Ning0612/Pi-Paper-Clock/tests/test_discord_notifier.py

import importlib.util
import json
import os
import sys
import tempfile
import types
import unittest
from pathlib import Path


class DiscordNotifierTests(unittest.TestCase):
    @classmethod
    def setUpClass(cls):
        names = ("network", "config_manager")
        cls.original_modules = {name: sys.modules.get(name) for name in names}

        network = types.ModuleType("network")
        network.STA_IF = 0
        network.WLAN = lambda _interface: types.SimpleNamespace(isconnected=lambda: False)
        sys.modules["network"] = network

        config_module = types.ModuleType("config_manager")
        config_module.config_manager = types.SimpleNamespace(
            get_global=lambda _key, default="": default,
            get=lambda _key, default=None: default,
        )
        sys.modules["config_manager"] = config_module

        source = Path(__file__).resolve().parents[1] / "src" / "discord_notifier.py"
        spec = importlib.util.spec_from_file_location("discord_notifier_test", source)
        cls.module = importlib.util.module_from_spec(spec)
        spec.loader.exec_module(cls.module)

    @classmethod
    def tearDownClass(cls):
        for name, module in cls.original_modules.items():
            if module is None:
                sys.modules.pop(name, None)
            else:
                sys.modules[name] = module

    def test_delivery_blocked_distinguishes_config_from_link_failures(self):
        config = sys.modules["config_manager"].config_manager
        original_get_global = config.get_global
        original_wlan = sys.modules["network"].WLAN
        try:
            config.get_global = lambda _key, default="": ""
            self.assertEqual(self.module.delivery_blocked(), "nowebhook")

            config.get_global = lambda _key, default="": "https://discord.com/api/webhooks/x/y"
            sys.modules["network"].WLAN = lambda _i: types.SimpleNamespace(
                isconnected=lambda: False
            )
            self.assertEqual(self.module.delivery_blocked(), "offline")

            sys.modules["network"].WLAN = lambda _i: types.SimpleNamespace(
                isconnected=lambda: True
            )
            self.assertEqual(self.module.delivery_blocked(), "")
        finally:
            config.get_global = original_get_global
            sys.modules["network"].WLAN = original_wlan

    def test_headroom_probe_reports_available_contiguous_block(self):
        self.assertTrue(self.module.has_tls_headroom(1024))
        self.assertEqual(self.module.largest_contiguous_block(4096), 4096)

    def test_diag_record_appends_and_trims_without_unbounded_growth(self):
        original_file = self.module.DIAG_FILE
        original_max = self.module.MAX_DIAG_BYTES
        with tempfile.TemporaryDirectory() as directory:
            self.module.DIAG_FILE = str(Path(directory) / "diag.log")
            self.module.MAX_DIAG_BYTES = 256
            try:
                for index in range(120):
                    self.module.diag_record("fail", "n={}".format(index))

                size = os.stat(self.module.DIAG_FILE).st_size
                self.assertLessEqual(size, self.module.MAX_DIAG_BYTES * 2)
                with open(self.module.DIAG_FILE) as handle:
                    lines = [line for line in handle.read().split("\n") if line]
                # Trimming drops the oldest half; the newest entry always survives.
                self.assertTrue(lines[-1].endswith("n=119"))
                self.assertIn("fail", lines[-1])
            finally:
                self.module.DIAG_FILE = original_file
                self.module.MAX_DIAG_BYTES = original_max

    def test_diag_record_never_raises_when_path_is_unwritable(self):
        original_file = self.module.DIAG_FILE
        self.module.DIAG_FILE = str(Path("no-such-dir") / "nested" / "diag.log")
        try:
            self.module.diag_record("fail", "unwritable")
        finally:
            self.module.DIAG_FILE = original_file

    def test_json_payload_escapes_controls_and_keeps_utf8_emoji(self):
        message = 'quote " slash \\ newline\n tab\t 中文🟦'
        payload = self.module._discord_payload(message)

        self.assertEqual(json.loads(payload.decode("utf-8")), {"content": message})
        self.assertIn("🟦".encode("utf-8"), payload)
        self.assertEqual(len(payload), len(payload.decode("utf-8").encode("utf-8")))

    def test_write_all_handles_partial_writes_without_copying_payload(self):
        class PartialSocket:
            def __init__(self):
                self.received = bytearray()

            def write(self, data):
                chunk = bytes(data[:2])
                self.received.extend(chunk)
                return len(chunk)

        sock = PartialSocket()
        self.module._write_all(sock, bytearray(b"abcdef"))
        self.assertEqual(sock.received, b"abcdef")

    def test_presence_embed_uses_exact_progress_colors_and_inline_fields(self):
        payload = self.module._presence_summary_embed_payload(
            "20260714", 51840, 7800, 4
        )
        embed = json.loads(payload.decode("utf-8"))["embeds"][0]

        self.assertEqual(embed["title"], "📊 在席日報 · 2026-07-14")
        self.assertEqual(embed["description"], "🟨🟨🟨🟨🟨🟨⬜⬜⬜⬜  60%")
        self.assertEqual(embed["color"], 15132194)
        self.assertEqual([field["name"] for field in embed["fields"]], ["書桌前", "最長一次", "次數"])
        self.assertTrue(all(field["inline"] for field in embed["fields"]))

    def test_progress_handles_negative_and_over_target_values(self):
        progress, percent, color = self.module._presence_progress(-1)
        self.assertEqual((progress, percent, color), ("⬜" * 10, 0, 15158332))

        progress, percent, color = self.module._presence_progress(86400 * 12)
        self.assertEqual((progress, percent, color), ("🟩" * 10, 999, 3066993))

    def test_the_autoreset_ip_note_is_consumed_on_read(self):
        """It must apply only to the boot its auto-reset caused.

        Left behind, a later power cycle would silently skip the online notice
        too, and the address would stop being announced at all.
        """
        original_file = self.module.AUTORESET_IP_FILE
        try:
            with tempfile.TemporaryDirectory() as directory:
                self.module.AUTORESET_IP_FILE = str(Path(directory) / "autoreset_ip.log")

                self.assertEqual(self.module.consume_autoreset_ip(), "")

                self.assertTrue(self.module.record_autoreset_ip("192.168.1.50"))
                self.assertEqual(self.module.consume_autoreset_ip(), "192.168.1.50")
                self.assertFalse(os.path.exists(self.module.AUTORESET_IP_FILE))
                self.assertEqual(self.module.consume_autoreset_ip(), "")
        finally:
            self.module.AUTORESET_IP_FILE = original_file

    def test_a_note_that_cannot_be_cleared_reports_nothing_consumed(self):
        """Left in place it would suppress the notice at every later boot with the
        same address, power cycles included.  One redundant notice beats silence."""
        original_file = self.module.AUTORESET_IP_FILE
        original_remove = os.remove
        try:
            with tempfile.TemporaryDirectory() as directory:
                self.module.AUTORESET_IP_FILE = str(Path(directory) / "autoreset_ip.log")
                self.module.record_autoreset_ip("192.168.1.50")

                def failing_remove(_path):
                    raise OSError(13, "denied")

                os.remove = failing_remove
                self.assertEqual(self.module.consume_autoreset_ip(), "")
        finally:
            os.remove = original_remove
            self.module.AUTORESET_IP_FILE = original_file

    def test_an_unwritable_autoreset_ip_note_is_not_fatal(self):
        """Failing to note it just means the next boot announces as usual."""
        original_file = self.module.AUTORESET_IP_FILE
        try:
            self.module.AUTORESET_IP_FILE = str(
                Path("no-such-dir") / "nested" / "autoreset_ip.log"
            )
            self.assertFalse(self.module.record_autoreset_ip("192.168.1.50"))
            self.assertEqual(self.module.consume_autoreset_ip(), "")
        finally:
            self.module.AUTORESET_IP_FILE = original_file

    def test_presence_session_message_uses_shared_l1_format(self):
        message = self.module._presence_session_message(
            "20260714", "090500", "20260715", "101500", 4200
        )
        self.assertEqual(message, "📖 書桌前時段結束\n09:05 → 10:15（1h 10m）")


if __name__ == "__main__":
    unittest.main()
